Elecrow-RD/CrowPanel-Advance-2.4-HMI-ESP32-S3-AI-Powered-IPS-Touch-Screen-320x240/example/V1.0/Arduino_Code/lesson-04/320_240/3.bmp

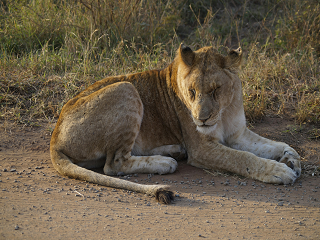
example/V1.0/Arduino_Code/lesson-04/320_240/3.bmp
