Elecrow-RD/CrowPanel-Advance-2.4-HMI-ESP32-S3-AI-Powered-IPS-Touch-Screen-320x240/example/V1.0/Thread/ot_brt/image/thread-border-router-esp32-esp32h2.jpg

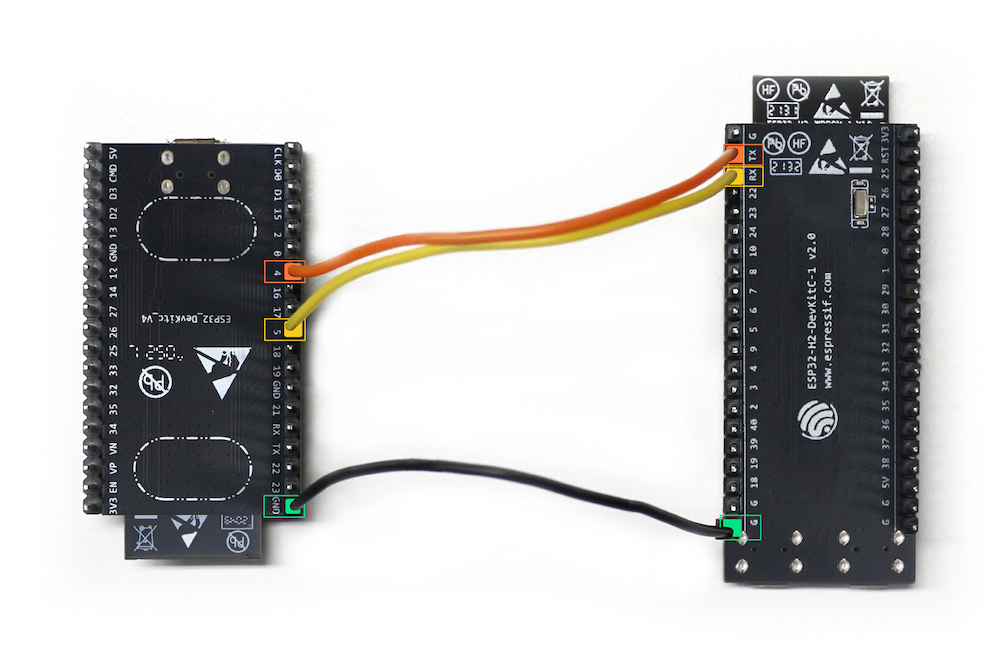
example/V1.0/Thread/ot_brt/image/thread-border-router-esp32-esp32h2.jpg
