Elecrow-RD/CrowPanel-Advance-2.4-HMI-ESP32-S3-AI-Powered-IPS-Touch-Screen-320x240/example/V1.1_and_V1.2/Mimiclaw/mimiclaw/assets/mimiclaw.png

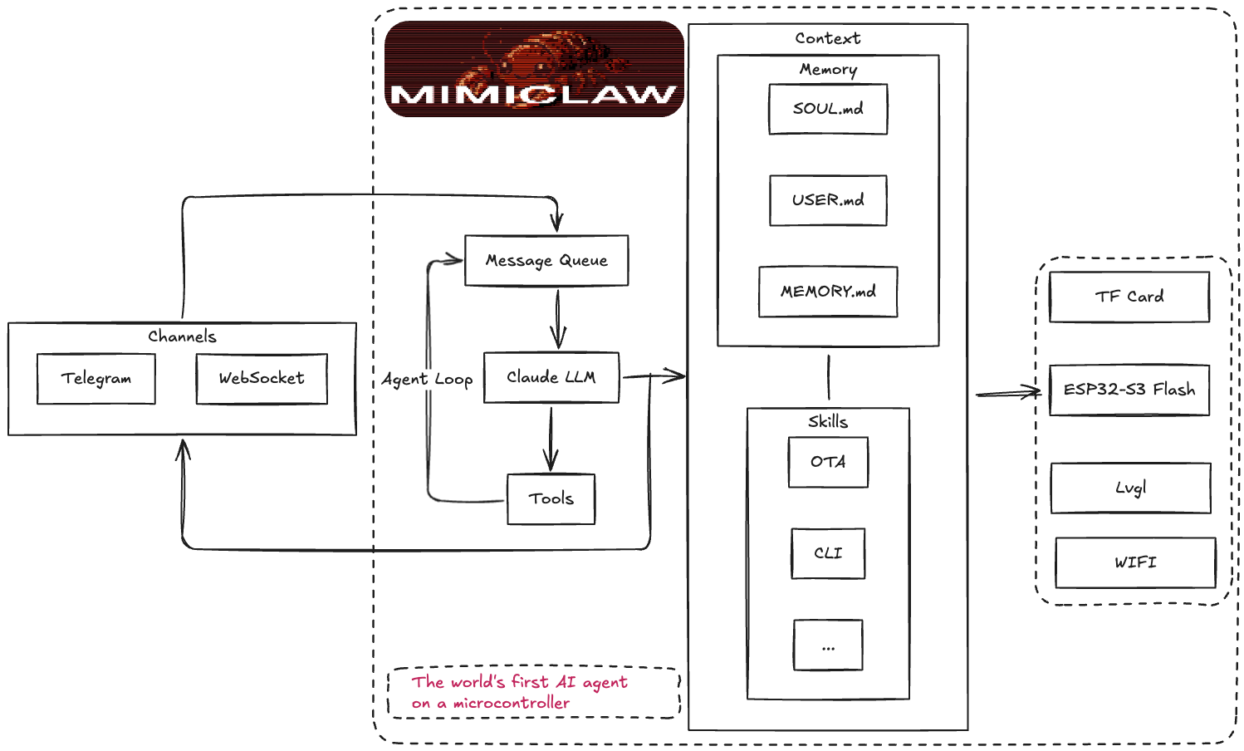
example/V1.1_and_V1.2/Mimiclaw/mimiclaw/assets/mimiclaw.png
